ittuann/iGEM-2022-NEFU_China/Code/Visual Identification Module/2.jpg

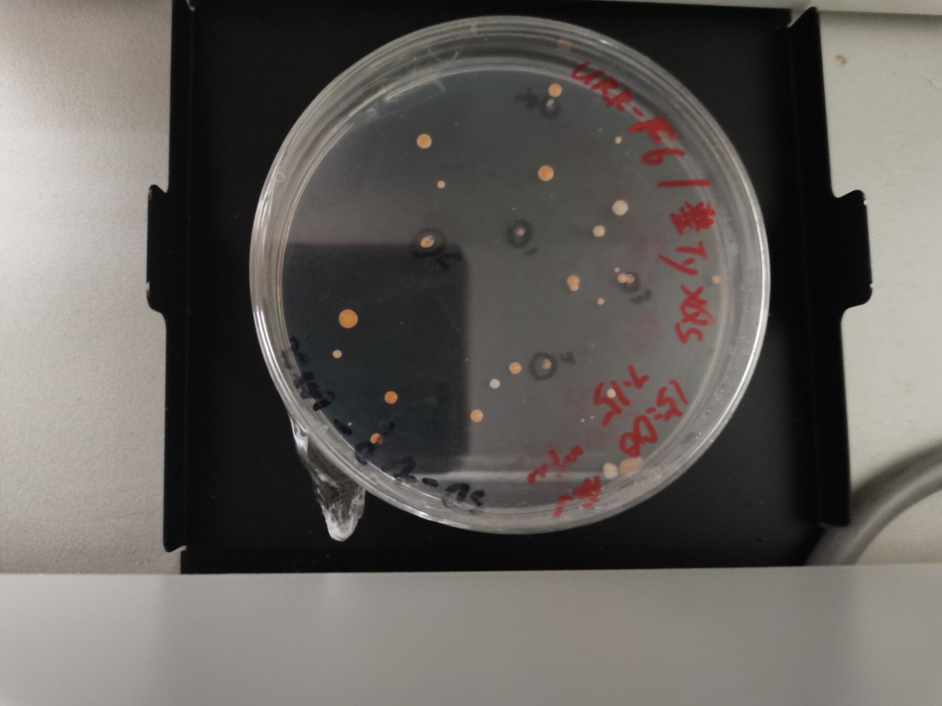
Code/Visual Identification Module/2.jpg
