ittuann/iGEM-2022-NEFU_China/Code/Visual Identification Module/11.jpg

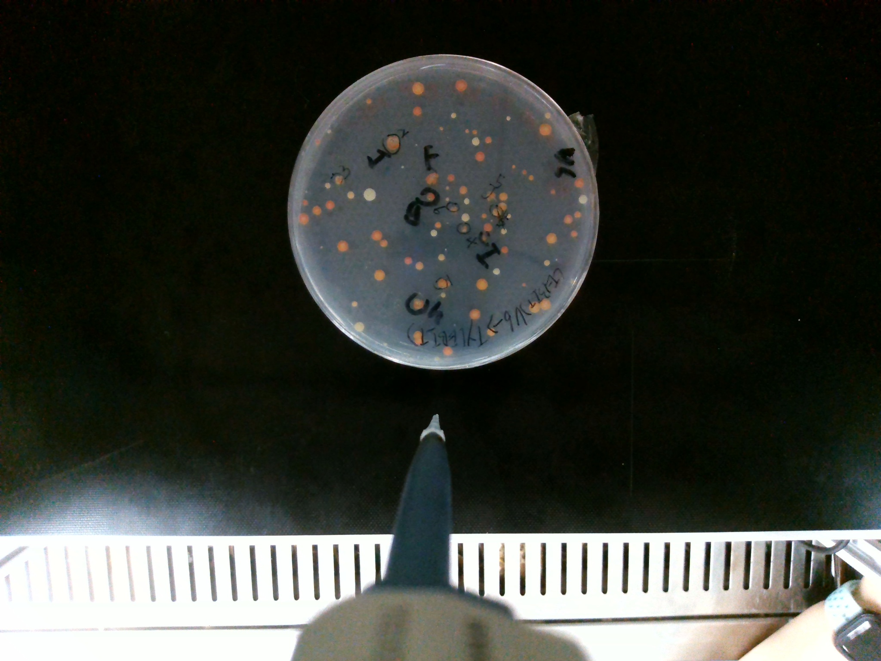
Code/Visual Identification Module/11.jpg
