ittuann/iGEM-2022-NEFU_China/Code/Visual Identification Module/13.jpg

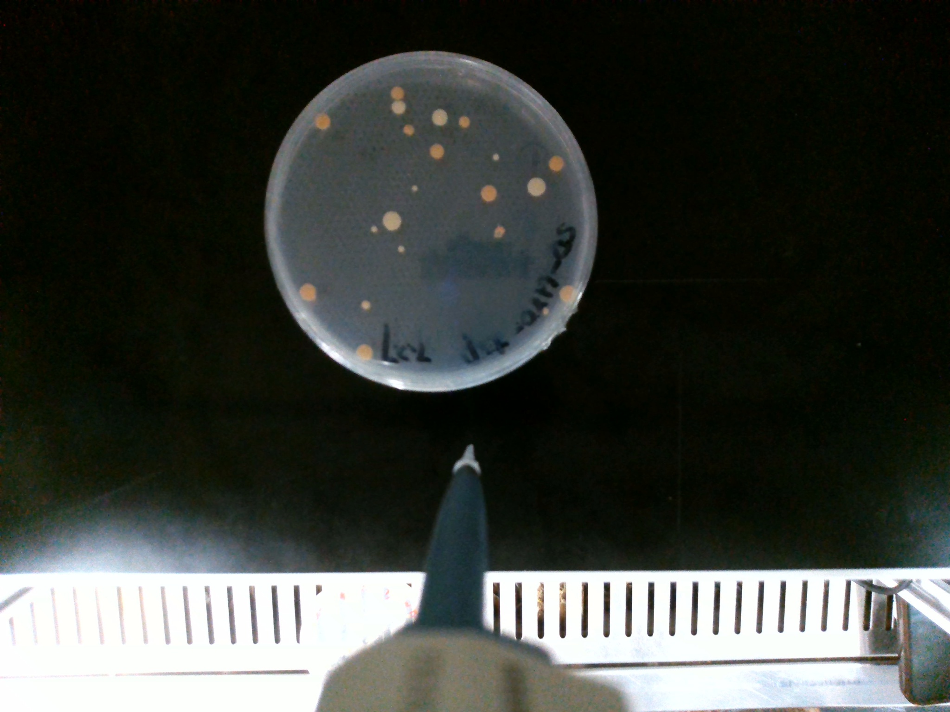
Code/Visual Identification Module/13.jpg
