ittuann/iGEM-2022-NEFU_China/Model/Project/圆盘组合A.SLDASM

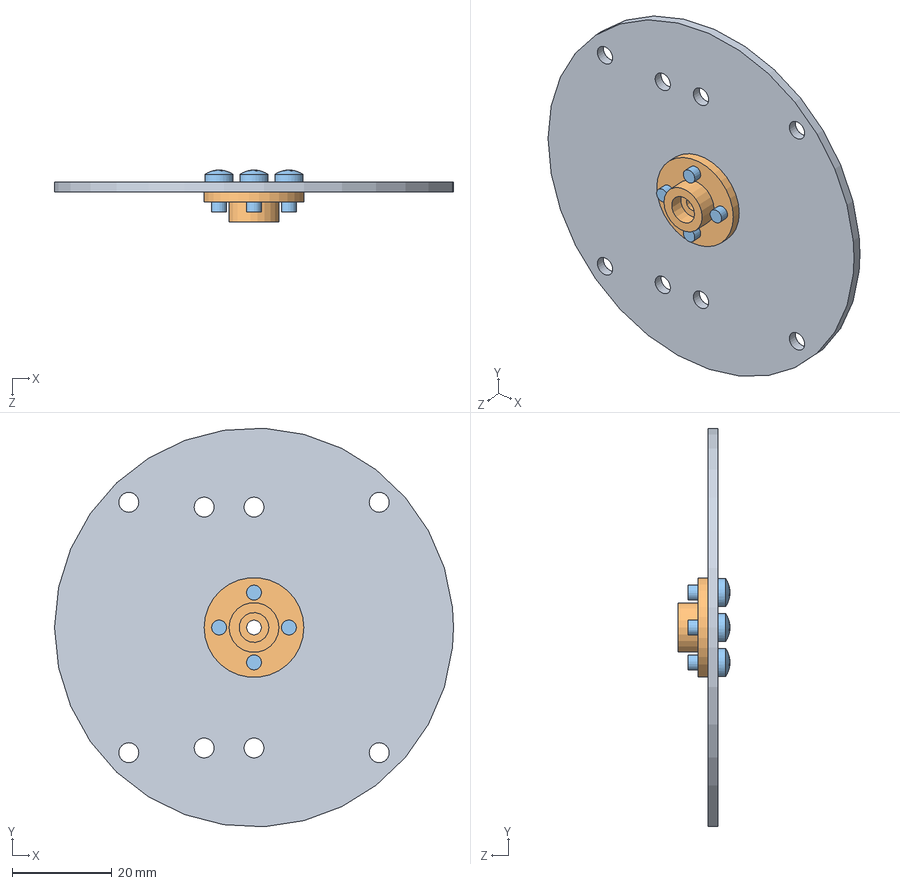
[picture p23: CAD file, 2022-10-12]
Model/Project/圆盘组合A.SLDASM
80.0 x 79.9 x 10.4 mm
小圆盘
金属舵盘
GB818-M3X6-ZN-4.8 x 4
