ittuann/iGEM-2022-NEFU_China/Model/Pipette Module.STL

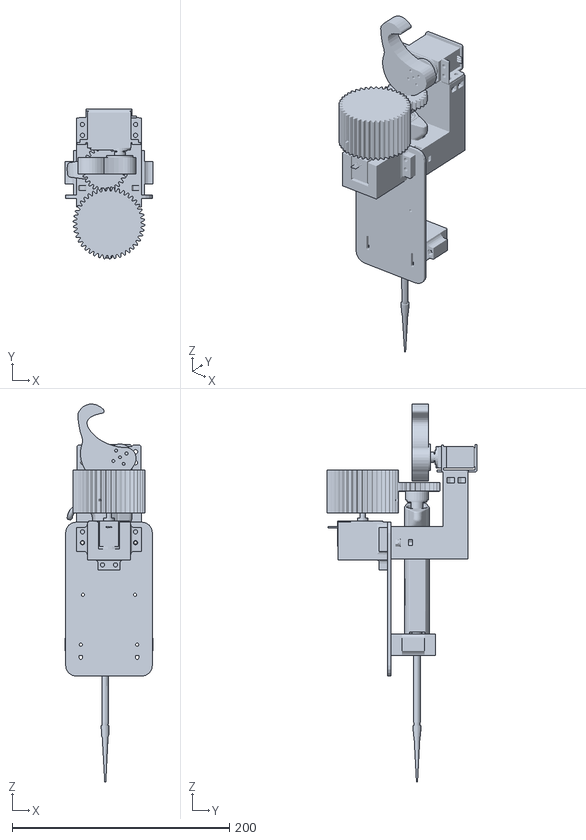
[picture p24: CAD file, 2022-10-11]
Model/Pipette Module.STL
81.0 x 138.3 x 348.2
