ittuann/iGEM-2022-NEFU_China/Model/Project/小舵机.SLDPRT

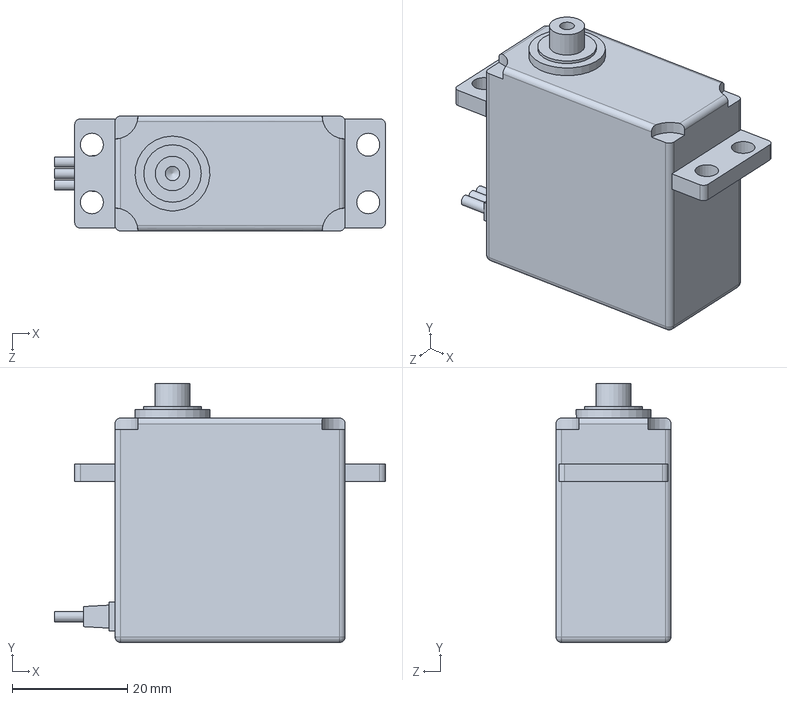
[picture p26: CAD file, 2022-10-12]
Model/Project/小舵机.SLDPRT
57.5 x 45.0 x 20.0 mm
