ittuann/iGEM-2022-NEFU_China/Model/Project/热端滑块.SLDPRT

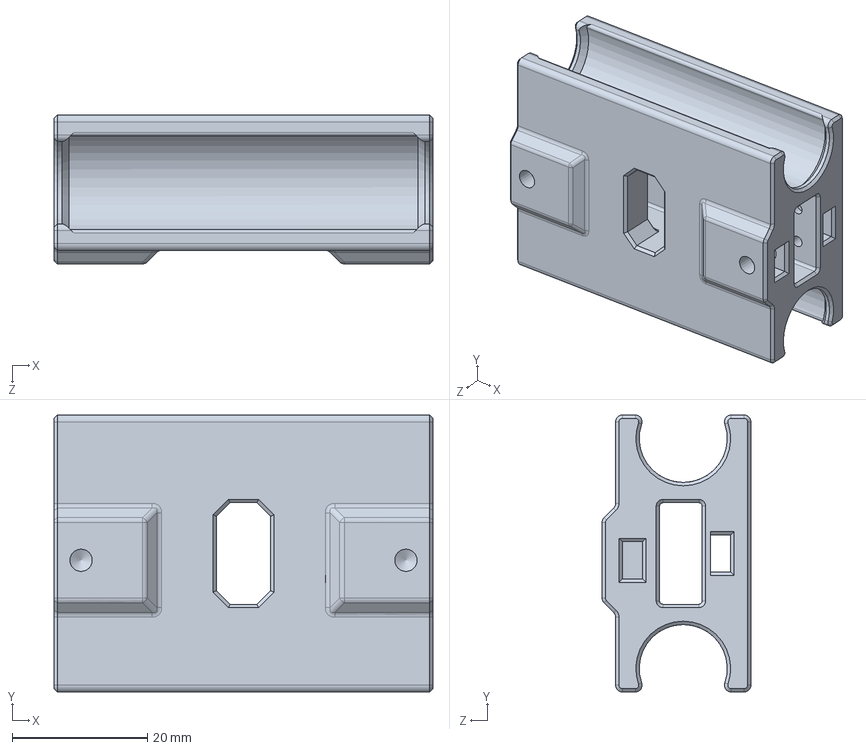
[picture p27: CAD file, 2022-10-12]
Model/Project/热端滑块.SLDPRT
56.0 x 40.9 x 22.0 mm
