ittuann/iGEM-2022-NEFU_China/Model/Project/221-BB-02-49 舵机座.SLDPRT

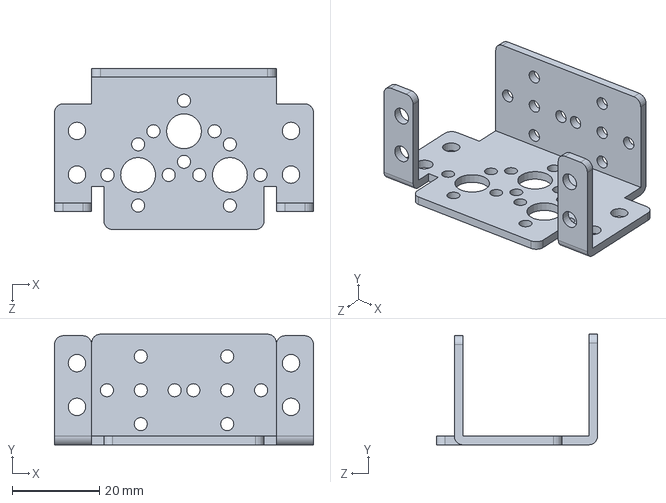
[picture p28: CAD file, 2022-10-12]
Model/Project/221-BB-02-49 舵机座.SLDPRT
59.3 x 25.4 x 36.9 mm
