ittuann/iGEM-2022-NEFU_China/Model/Project/GB818-M3X10-ZN-4.8.SLDPRT

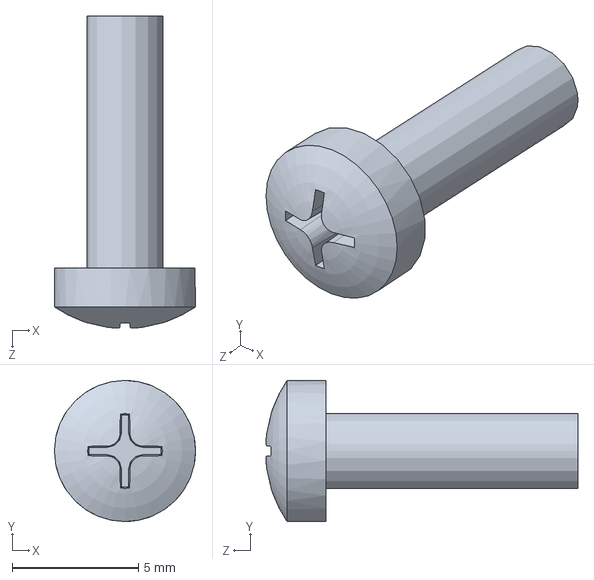
[picture p29: CAD file, 2022-10-12]
Model/Project/GB818-M3X10-ZN-4.8.SLDPRT
5.60 x 5.60 x 12.4 mm
