ittuann/iGEM-2022-NEFU_China/Model/Project/同步带2.SLDPRT

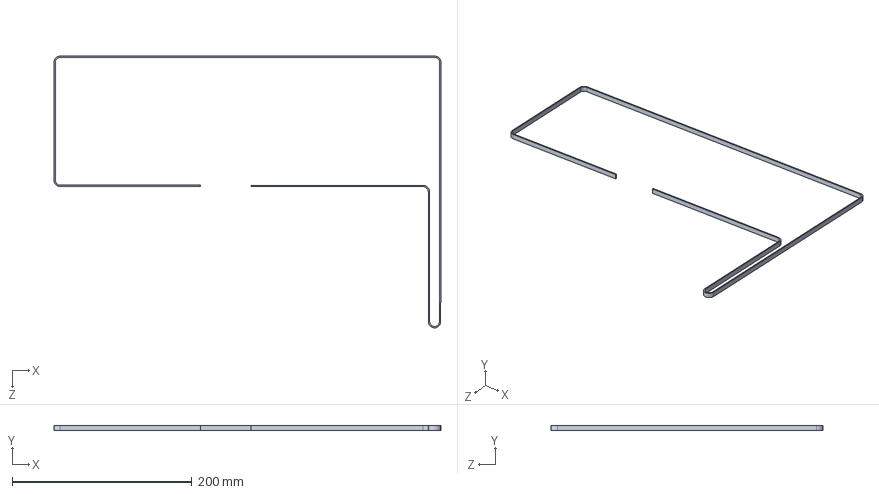
[picture p30: CAD file, 2022-10-12]
Model/Project/同步带2.SLDPRT
431.1 x 6.00 x 302.8 mm
