ittuann/iGEM-2022-NEFU_China/Model/Project/安装扣.SLDPRT

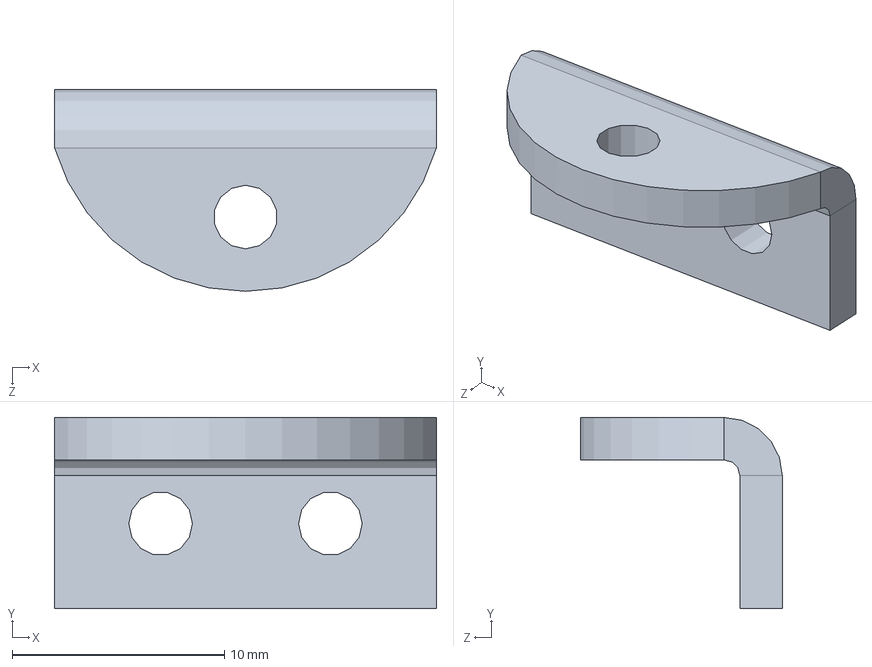
[picture p31: CAD file, 2022-10-12]
Model/Project/安装扣.SLDPRT
18.0 x 9.00 x 9.50 mm
