ittuann/iGEM-2022-NEFU_China/Model/Project/Корпус.SLDPRT

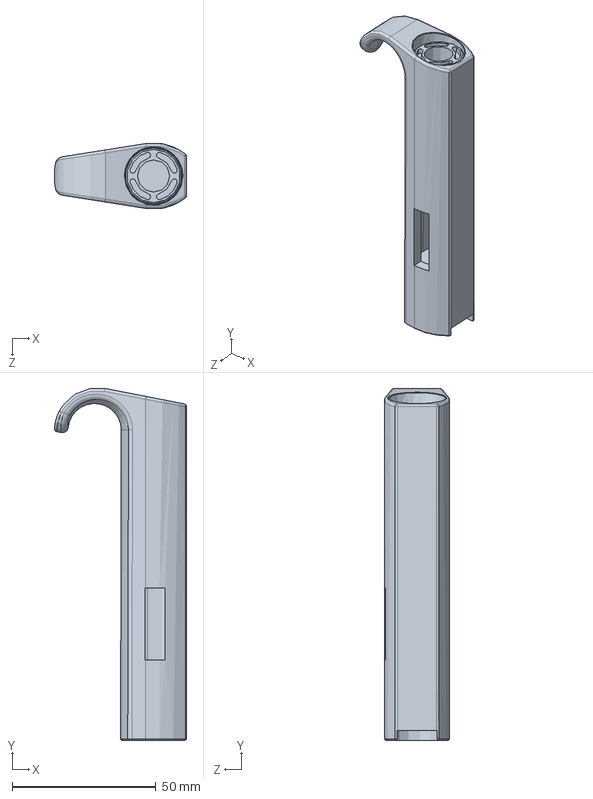
[picture p32: CAD file, 2022-10-12]
Model/Project/Корпус.SLDPRT
46.0 x 122.5 x 22.8 mm
