ittuann/iGEM-2022-NEFU_China/Model/Project/爪子齿轮.SLDPRT

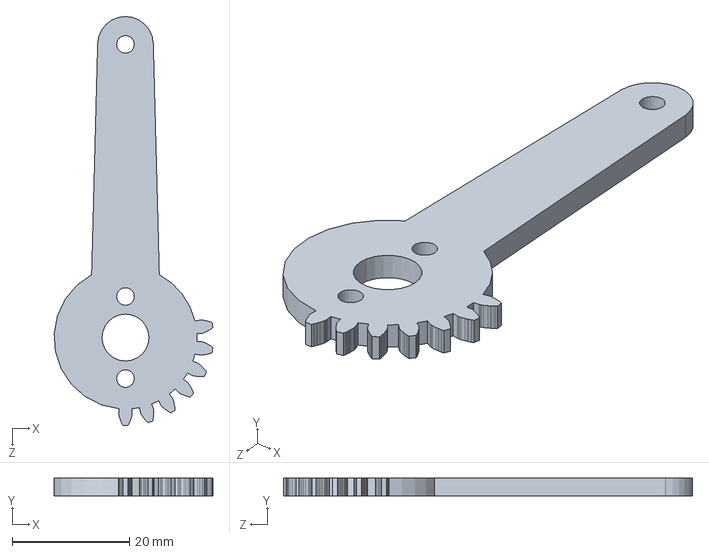
[picture p33: CAD file, 2022-10-12]
Model/Project/爪子齿轮.SLDPRT
27.1 x 3.00 x 69.7 mm
