ittuann/iGEM-2022-NEFU_China/Model/Project/JXS007.SLDPRT

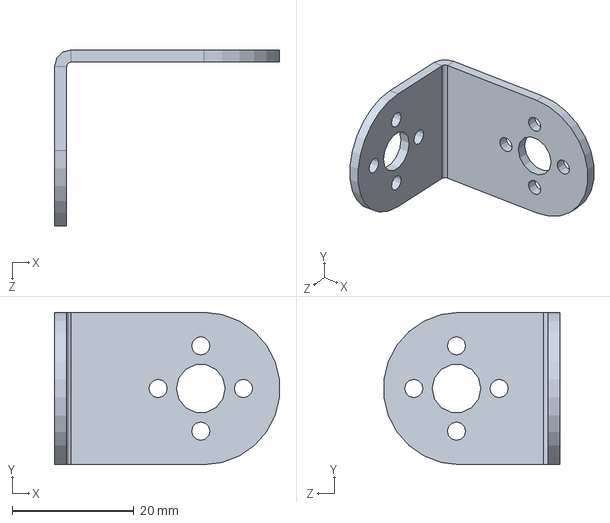
[picture p34: CAD file, 2022-10-12]
Model/Project/JXS007.SLDPRT
36.9 x 25.0 x 28.9 mm
