ittuann/iGEM-2022-NEFU_China/Model/Project/大轴承.SLDPRT

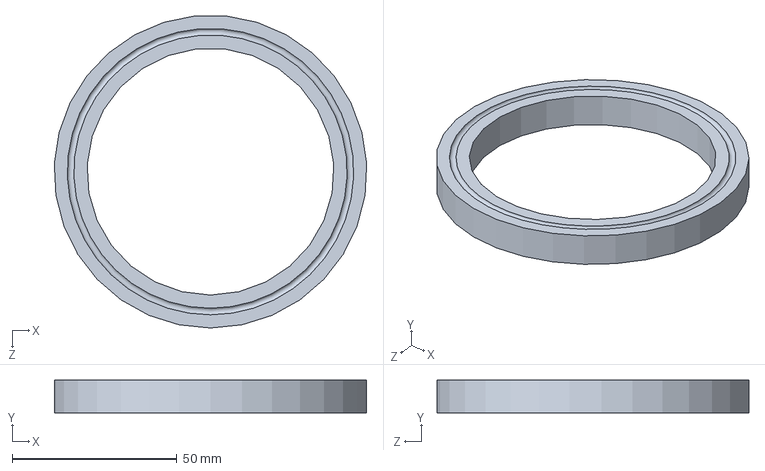
[picture p35: CAD file, 2022-10-12]
Model/Project/大轴承.SLDPRT
94.9 x 10.0 x 94.8 mm
