ittuann/iGEM-2022-NEFU_China/Model/Project/光轴支架_右上.SLDPRT

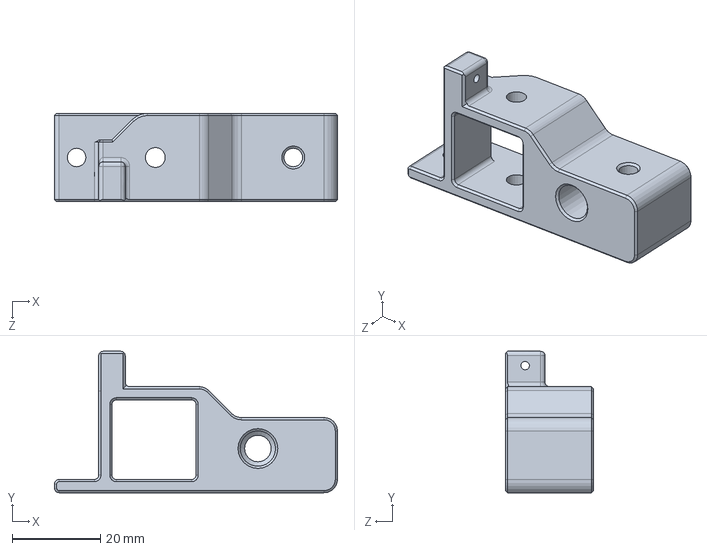
[picture p36: CAD file, 2022-10-12]
Model/Project/光轴支架_右上.SLDPRT
64.0 x 32.0 x 20.0 mm
