ittuann/iGEM-2022-NEFU_China/Model/Project/35BYJ电机座.SLDPRT

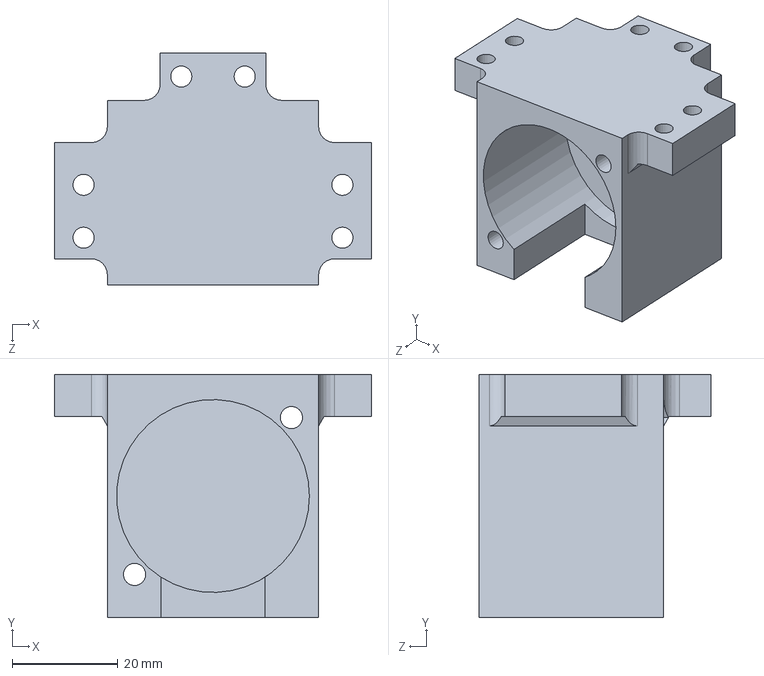
[picture p37: CAD file, 2022-10-12]
Model/Project/35BYJ电机座.SLDPRT
60.0 x 46.0 x 44.0 mm
