ittuann/iGEM-2022-NEFU_China/Model/Project/圆环.SLDPRT

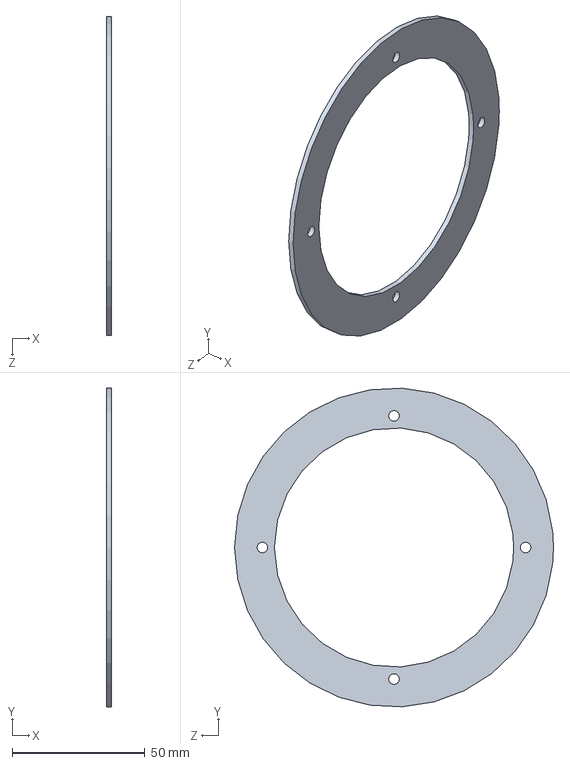
[picture p39: CAD file, 2022-10-12]
Model/Project/圆环.SLDPRT
2.00 x 119.8 x 120.0 mm
