ittuann/iGEM-2022-NEFU_China/Model/Project/大圆柱齿轮42×1.5.SLDPRT

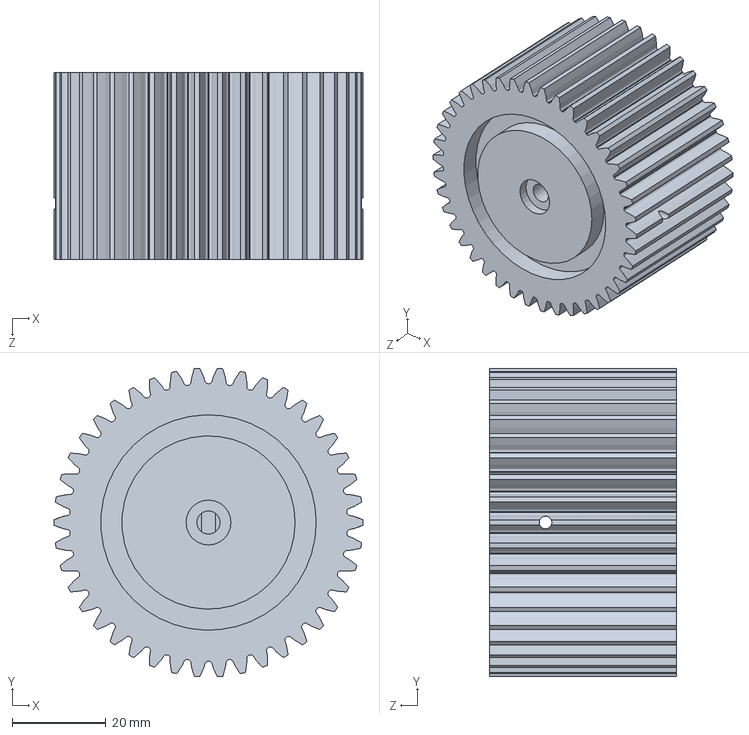
[picture p40: CAD file, 2022-10-12]
Model/Project/大圆柱齿轮42×1.5.SLDPRT
66.0 x 65.9 x 40.0 mm
