ittuann/iGEM-2022-NEFU_China/Model/Project/GB818-M3X14-ZN-4.8.SLDPRT

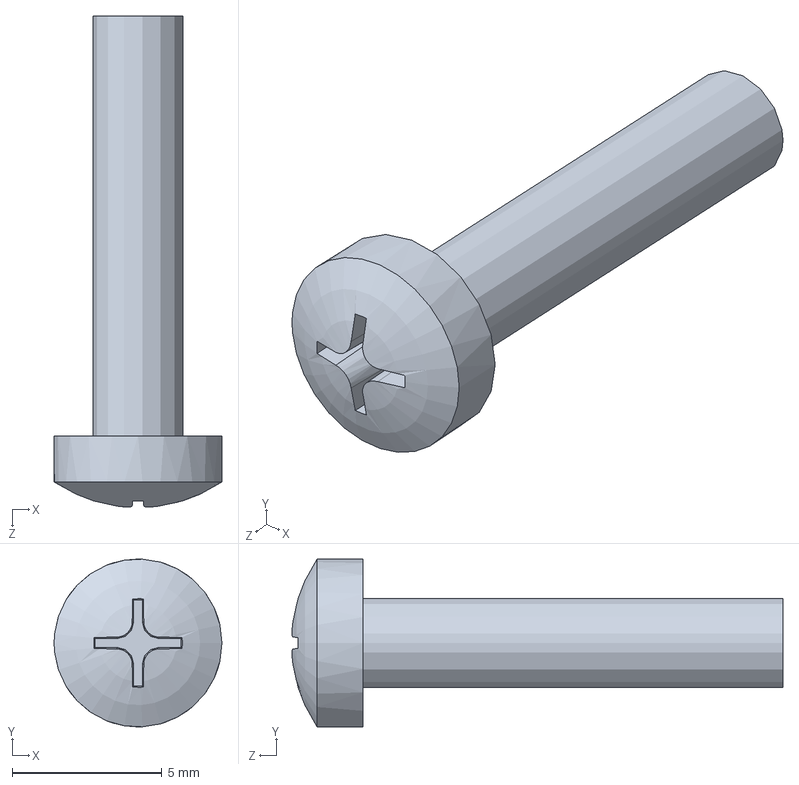
[picture p41: CAD file, 2022-10-12]
Model/Project/GB818-M3X14-ZN-4.8.SLDPRT
5.60 x 5.60 x 16.4 mm
