ittuann/iGEM-2022-NEFU_China/Model/Project/Z轴限位开关支架（2件）.SLDPRT

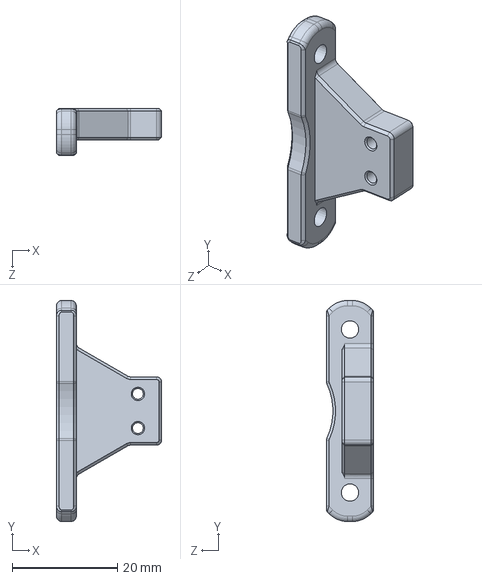
[picture p42: CAD file, 2022-10-12]
Model/Project/Z轴限位开关支架（2件）.SLDPRT
20.0 x 42.0 x 9.00 mm
