ittuann/iGEM-2022-NEFU_China/Model/Project/Кнопка экстрактора.SLDPRT

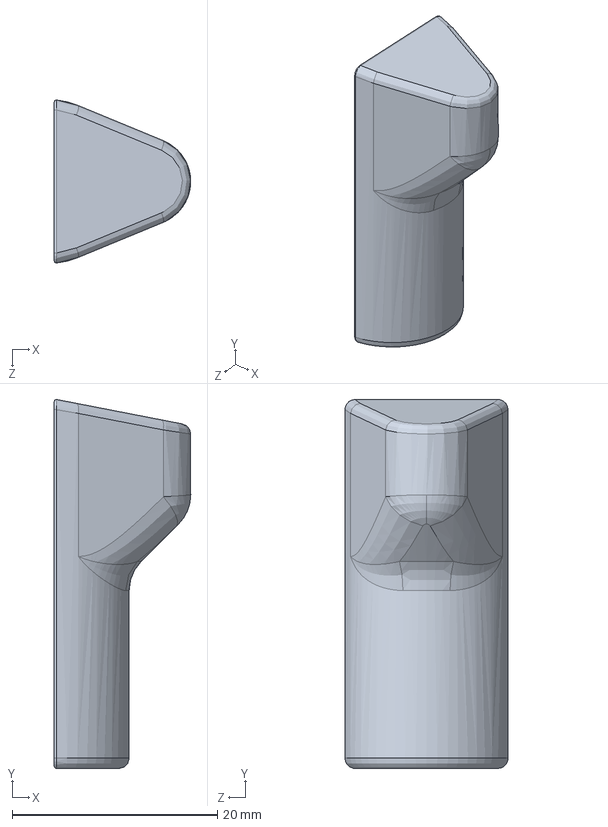
[picture p44: CAD file, 2022-10-12]
Model/Project/Кнопка экстрактора.SLDPRT
13.3 x 36.0 x 15.9 mm
