ittuann/iGEM-2022-NEFU_China/Model/Project/长杆.SLDPRT

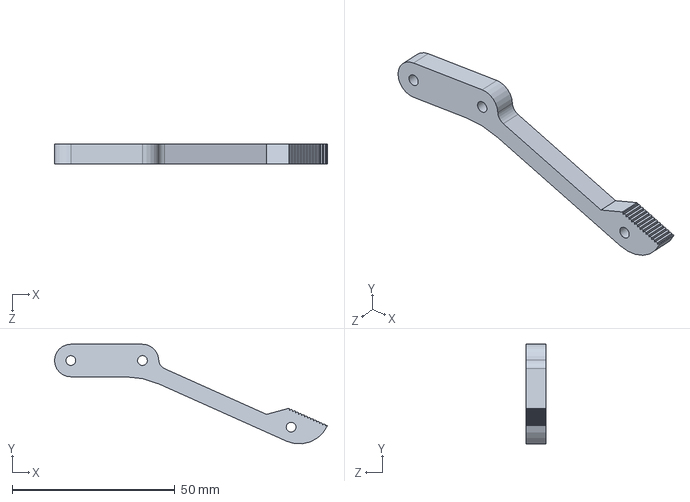
[picture p45: CAD file, 2022-10-12]
Model/Project/长杆.SLDPRT
83.8 x 30.5 x 6.00 mm
