ittuann/iGEM-2022-NEFU_China/Model/Project/光轴支架_左下.SLDPRT

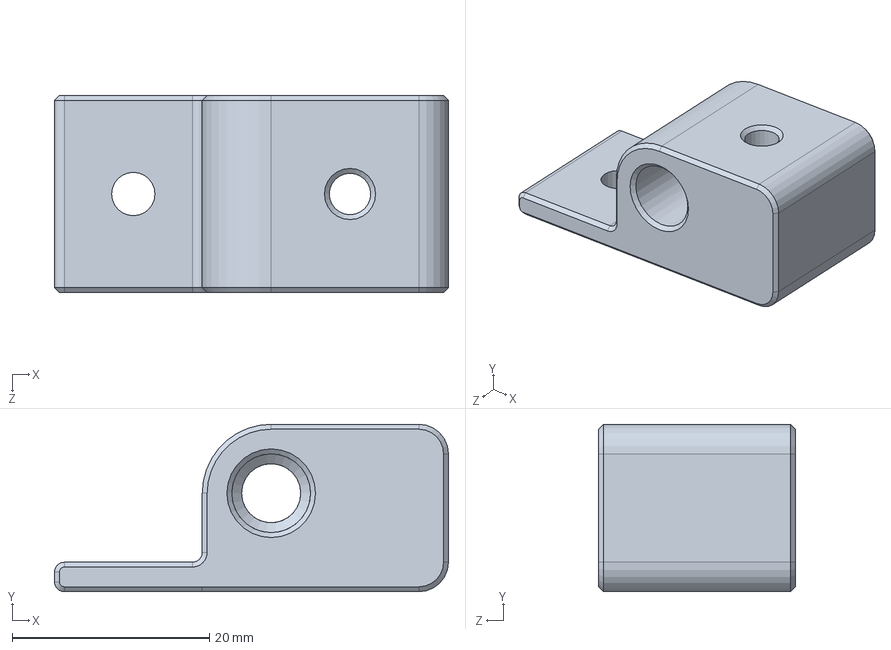
[picture p46: CAD file, 2022-10-12]
Model/Project/光轴支架_左下.SLDPRT
40.0 x 17.0 x 20.0 mm
