ittuann/iGEM-2022-NEFU_China/Model/Project/X轴光轴座_右.SLDPRT

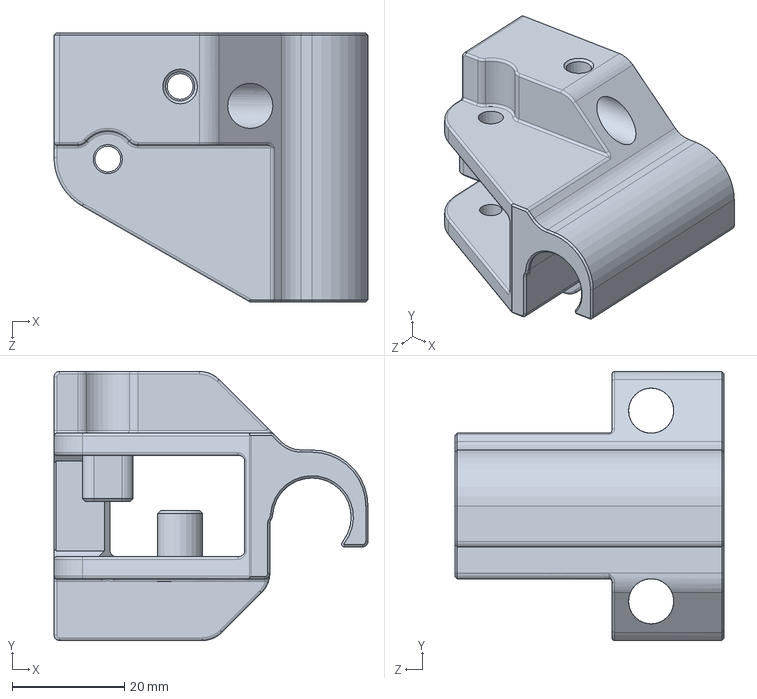
[picture p47: CAD file, 2022-10-12]
Model/Project/X轴光轴座_右.SLDPRT
56.0 x 48.0 x 48.0 mm
