ittuann/iGEM-2022-NEFU_China/Model/Project/圆柱齿轮小.SLDPRT

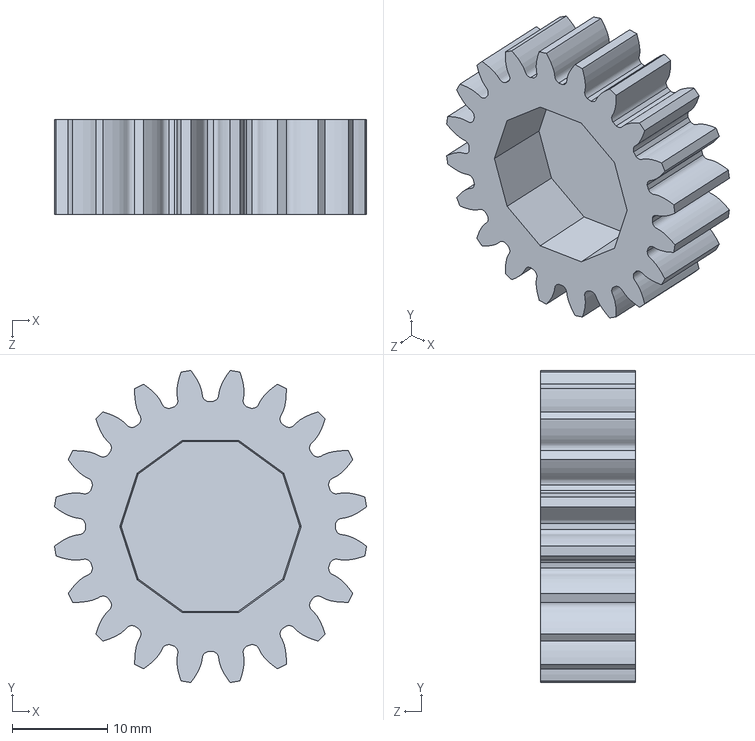
[picture p48: CAD file, 2022-10-12]
Model/Project/圆柱齿轮小.SLDPRT
32.7 x 32.7 x 10.0 mm
