ittuann/iGEM-2022-NEFU_China/Model/Project/JXS005.SLDPRT

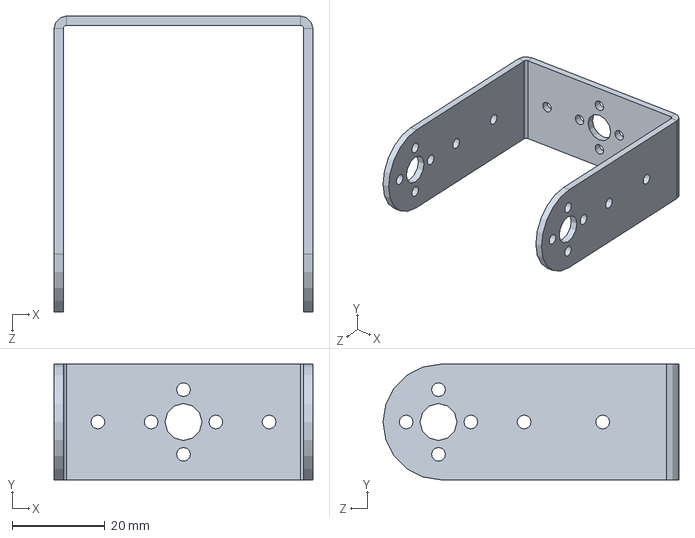
[picture p49: CAD file, 2022-10-12]
Model/Project/JXS005.SLDPRT
56.0 x 25.0 x 64.0 mm
