ittuann/iGEM-2022-NEFU_China/Model/Project/小横杆.SLDPRT

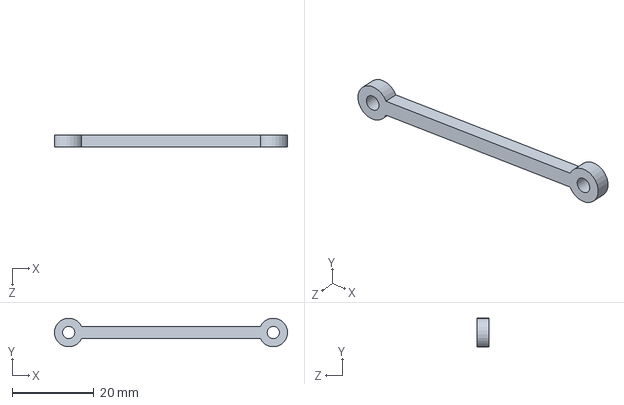
[picture p50: CAD file, 2022-10-12]
Model/Project/小横杆.SLDPRT
56.9 x 6.97 x 3.00 mm
