ittuann/iGEM-2022-NEFU_China/Model/Project/42步进电机.SLDPRT

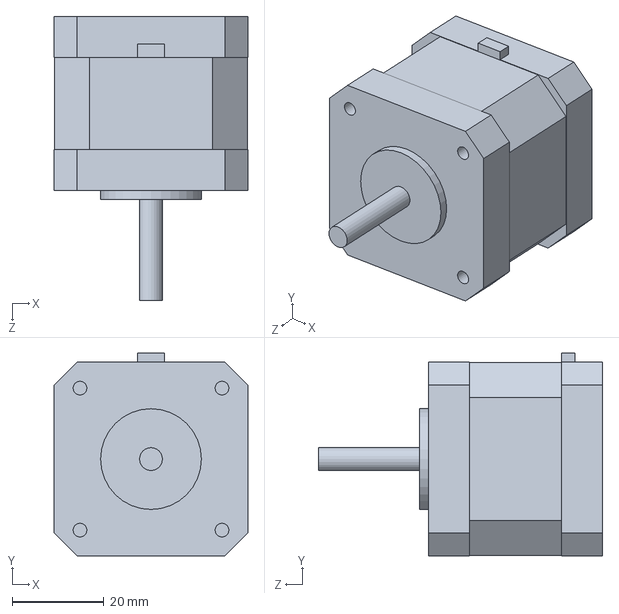
[picture p52: CAD file, 2022-10-12]
Model/Project/42步进电机.SLDPRT
42.3 x 44.3 x 62.0 mm
