ittuann/iGEM-2022-NEFU_China/Model/Project/小圆盘.SLDPRT

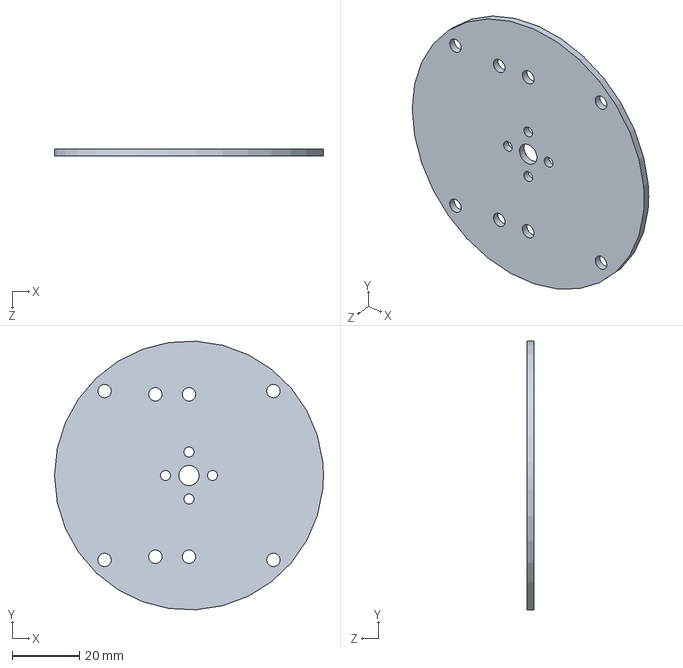
[picture p53: CAD file, 2022-10-12]
Model/Project/小圆盘.SLDPRT
80.0 x 79.9 x 2.00 mm
