ittuann/iGEM-2022-NEFU_China/Model/Project/舵机连接独立.SLDPRT

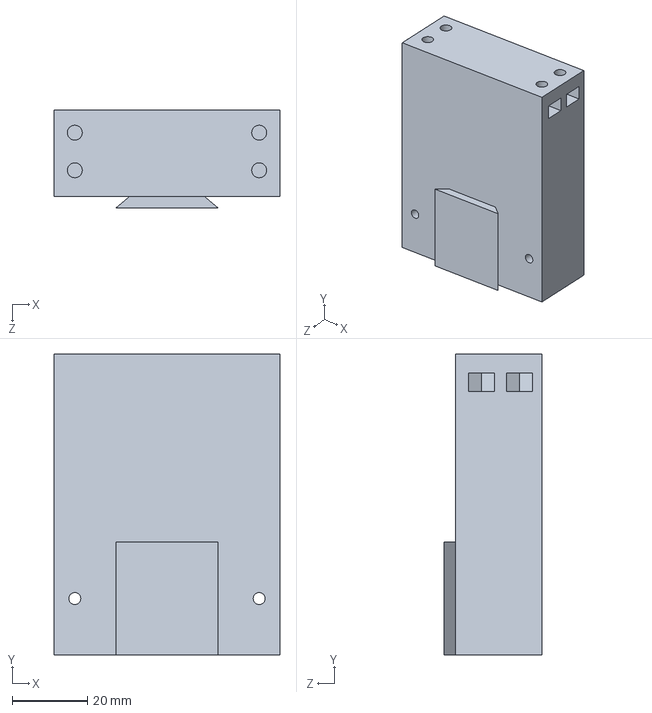
[picture p54: CAD file, 2022-10-12]
Model/Project/舵机连接独立.SLDPRT
60.0 x 80.0 x 26.0 mm
