ittuann/iGEM-2022-NEFU_China/Model/Project/圆柱齿轮26×1.5.SLDPRT

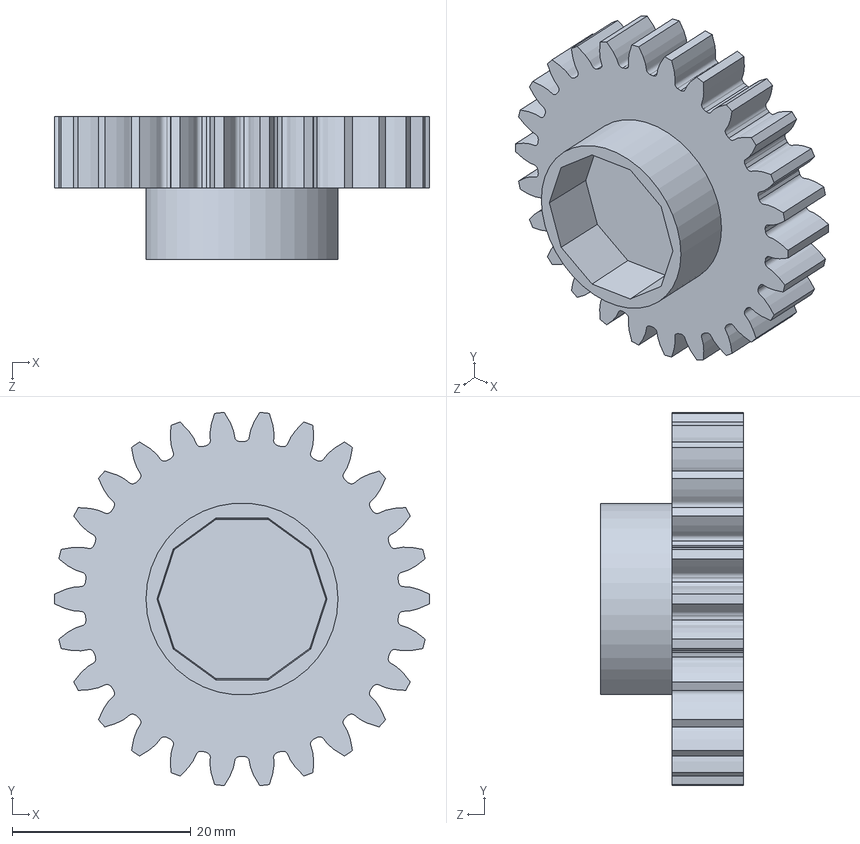
[picture p55: CAD file, 2022-10-12]
Model/Project/圆柱齿轮26×1.5.SLDPRT
42.0 x 41.8 x 16.0 mm
