ittuann/iGEM-2022-NEFU_China/Model/Project/小垫片.SLDPRT

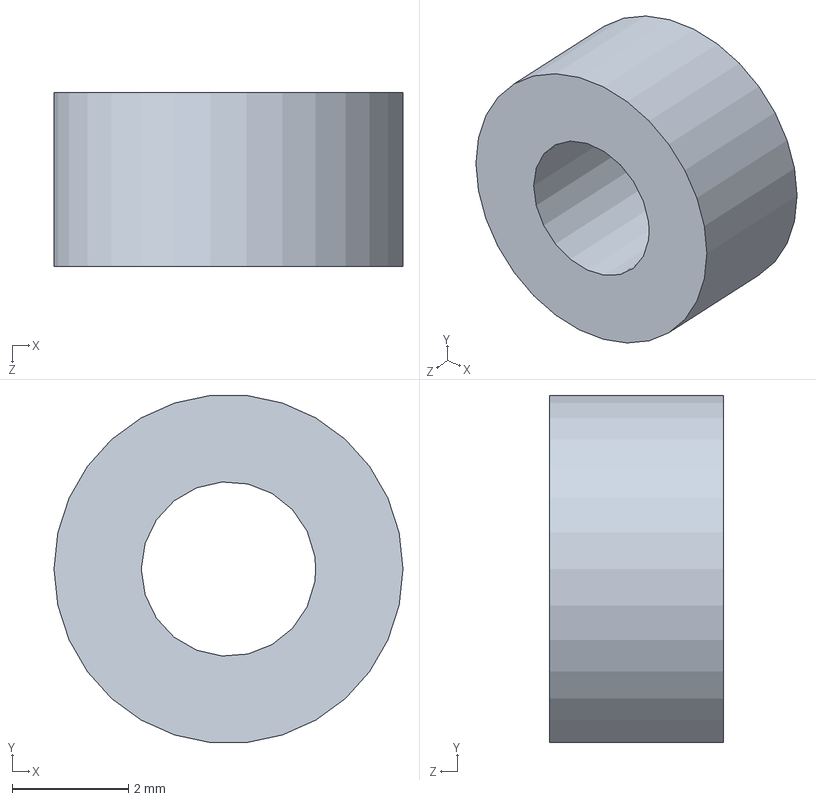
[picture p56: CAD file, 2022-10-12]
Model/Project/小垫片.SLDPRT
6.00 x 5.97 x 3.00 mm
