ittuann/iGEM-2022-NEFU_China/Model/Project/中心配重块.SLDPRT

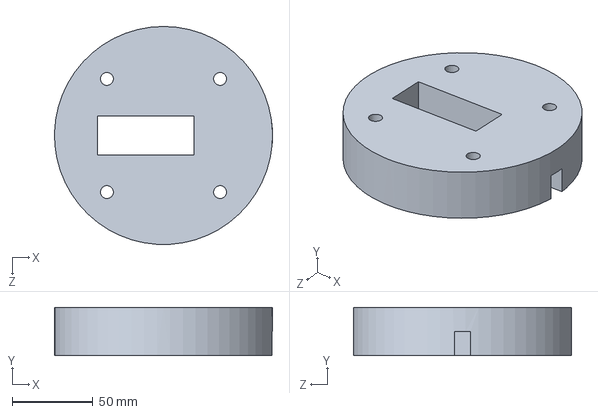
[picture p57: CAD file, 2022-10-12]
Model/Project/中心配重块.SLDPRT
134.9 x 30.0 x 135.0 mm
