ittuann/iGEM-2022-NEFU_China/Model/Project/连接板.SLDPRT

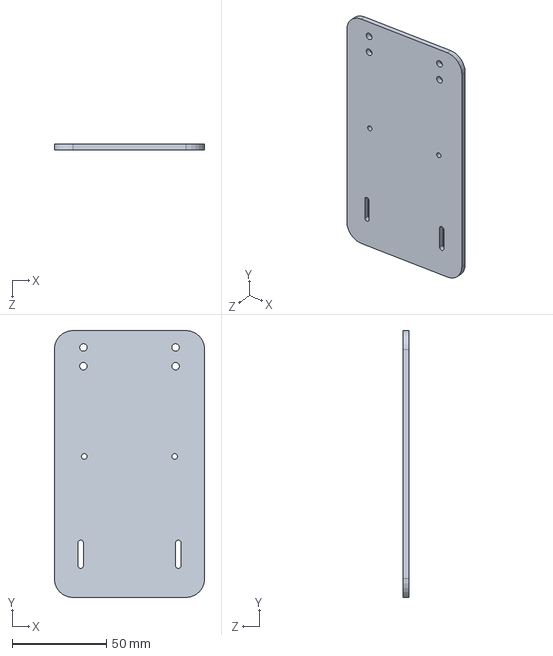
[picture p58: CAD file, 2022-10-12]
Model/Project/连接板.SLDPRT
80.0 x 142.0 x 3.00 mm
