ittuann/iGEM-2022-NEFU_China/Model/Project/底板.SLDPRT

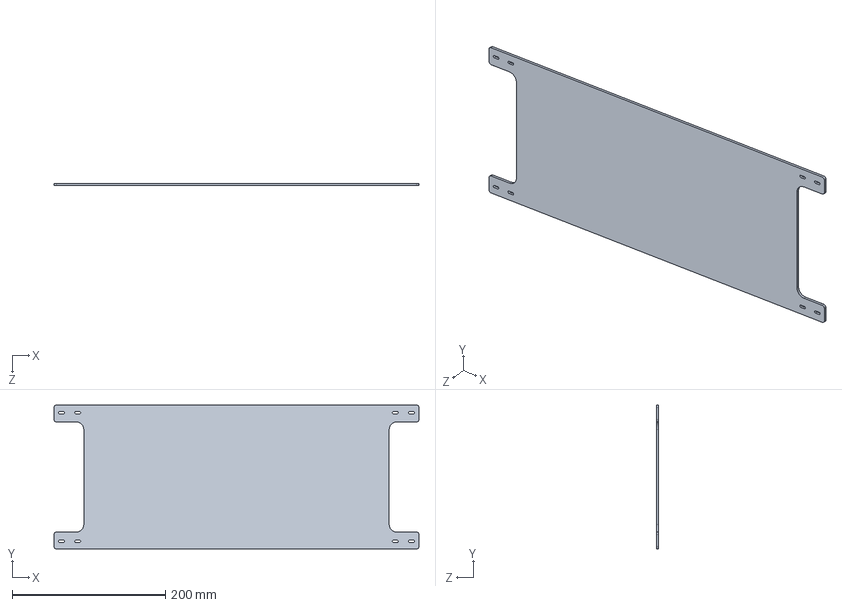
[picture p59: CAD file, 2022-10-12]
Model/Project/底板.SLDPRT
477.0 x 188.0 x 3.00 mm
