ittuann/iGEM-2022-NEFU_China/Model/Project/中心配重块上层.SLDPRT

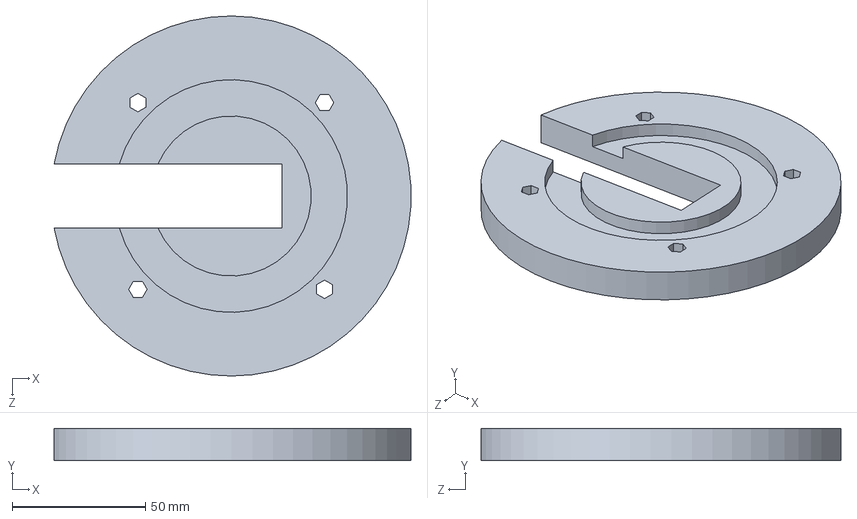
[picture p60: CAD file, 2022-10-12]
Model/Project/中心配重块上层.SLDPRT
133.8 x 12.0 x 135.0 mm
