ittuann/iGEM-2022-NEFU_China/Model/Project/Игла.SLDPRT

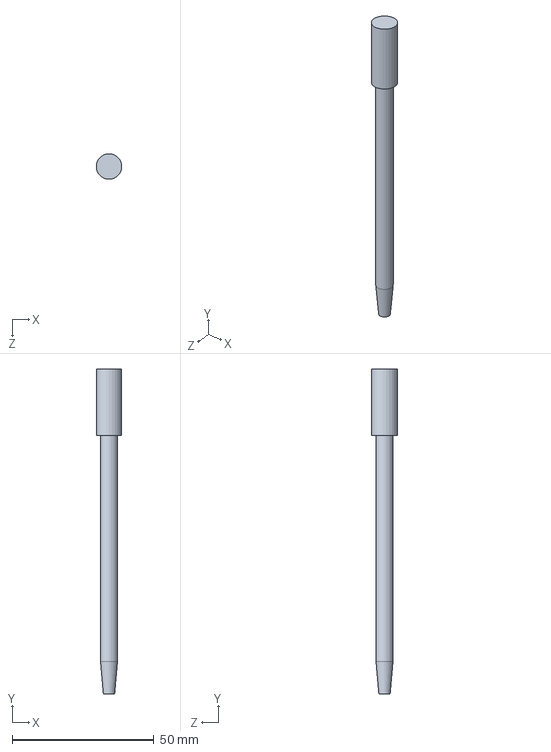
[picture p61: CAD file, 2022-10-12]
Model/Project/Игла.SLDPRT
8.93 x 114.5 x 9.00 mm
