ittuann/iGEM-2022-NEFU_China/Model/Project/Наконечник иглы.SLDPRT

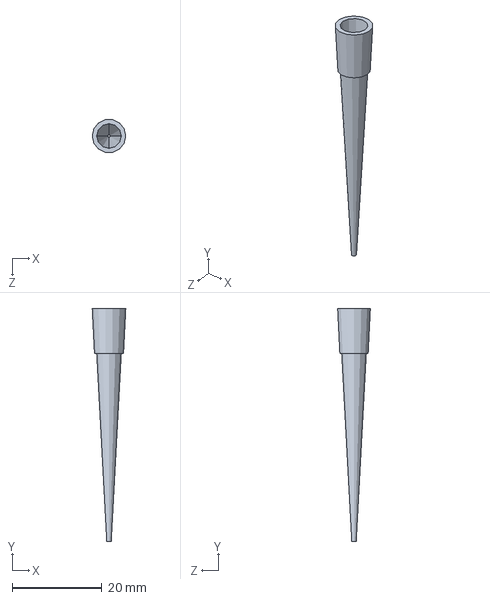
[picture p62: CAD file, 2022-10-12]
Model/Project/Наконечник иглы.SLDPRT
7.50 x 52.0 x 7.31 mm
