ittuann/iGEM-2022-NEFU_China/Model/Project/铝基板热床200×300×3.SLDPRT

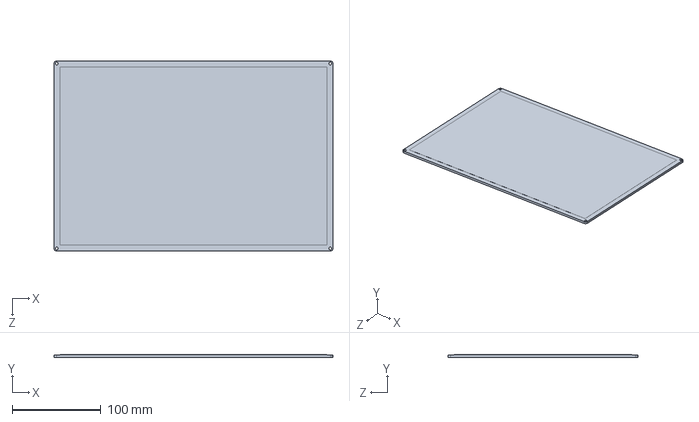
[picture p63: CAD file, 2022-10-12]
Model/Project/铝基板热床200×300×3.SLDPRT
314.0 x 3.20 x 214.0 mm
