ittuann/iGEM-2022-NEFU_China/Model/Project/杯士轴承.SLDPRT

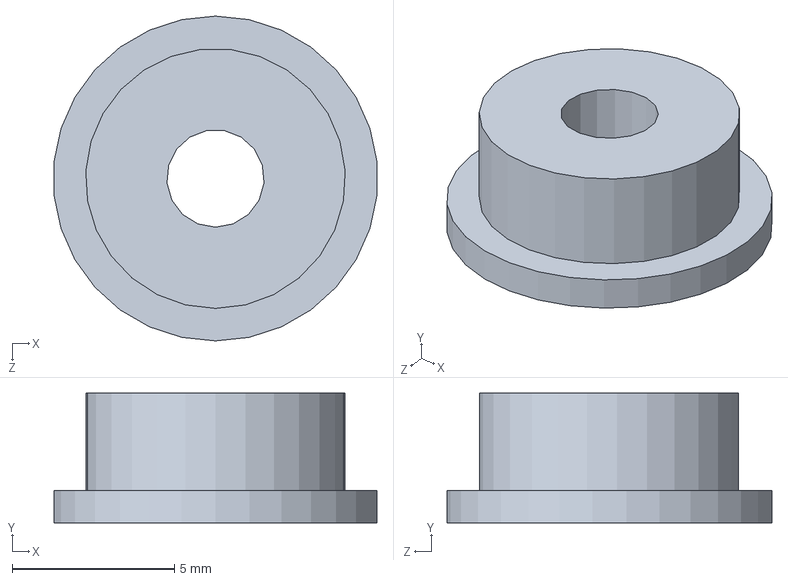
[picture p64: CAD file, 2022-10-12]
Model/Project/杯士轴承.SLDPRT
9.95 x 4.00 x 10.0 mm
