ittuann/iGEM-2022-NEFU_China/Model/Project/35BYJ412.SLDPRT

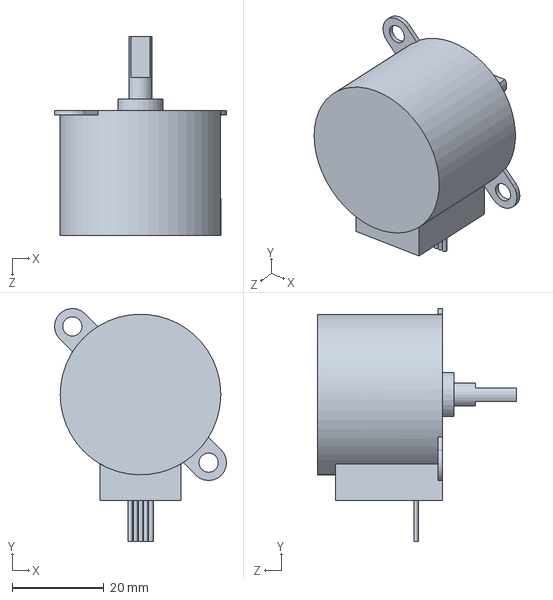
[picture p65: CAD file, 2022-10-12]
Model/Project/35BYJ412.SLDPRT
37.5 x 50.8 x 43.4 mm
