ittuann/iGEM-2022-NEFU_China/Model/Project/底部圆盘.SLDPRT

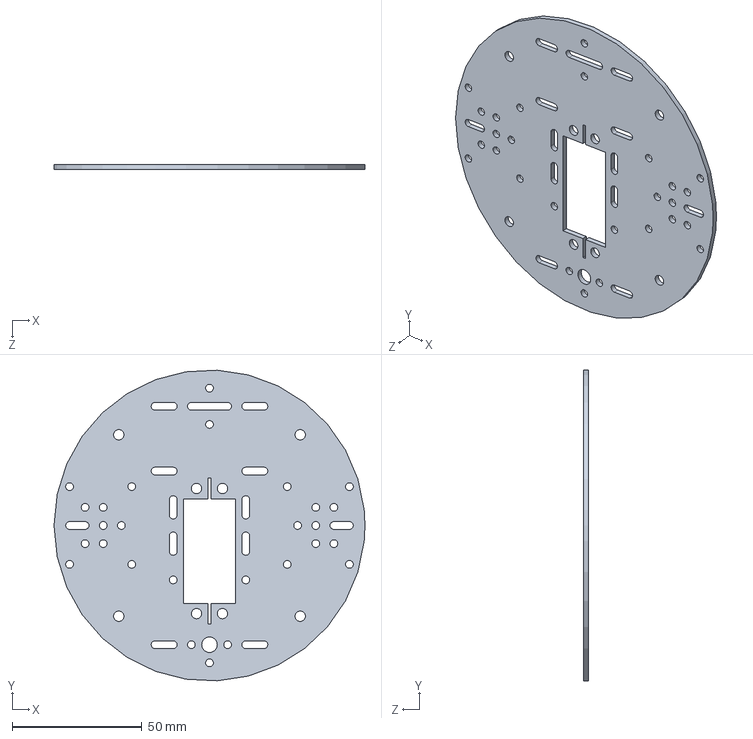
[picture p66: CAD file, 2022-10-12]
Model/Project/底部圆盘.SLDPRT
120.0 x 119.8 x 2.00 mm
