ittuann/iGEM-2022-NEFU_China/Model/Project/惠普电源DPS-460EB A.SLDPRT

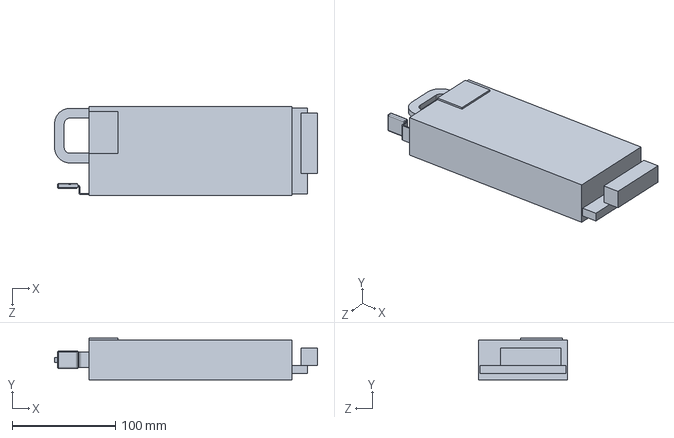
[picture p67: CAD file, 2022-10-12]
Model/Project/惠普电源DPS-460EB A.SLDPRT
254.5 x 40.5 x 86.5 mm
