ittuann/iGEM-2022-NEFU_China/Model/Project/螺柱.SLDPRT

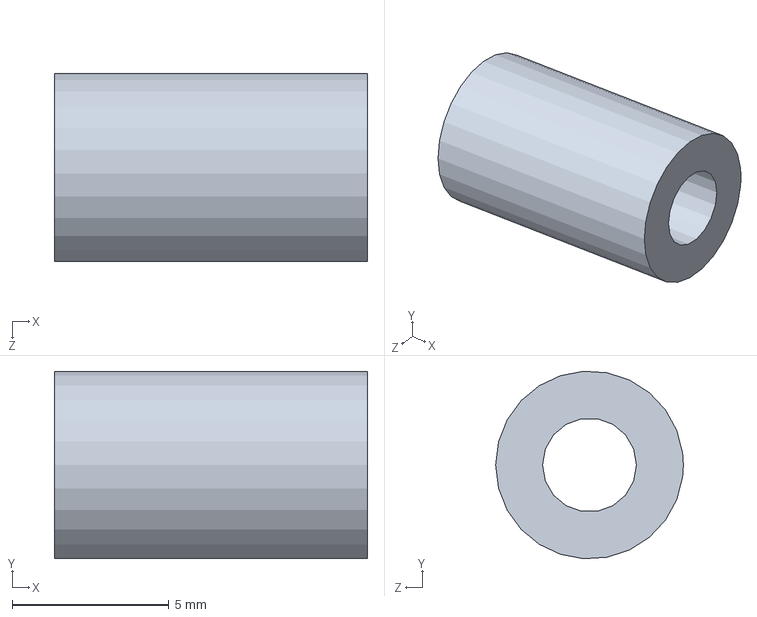
[picture p68: CAD file, 2022-10-12]
Model/Project/螺柱.SLDPRT
10.0 x 5.99 x 6.00 mm
