ittuann/iGEM-2022-NEFU_China/Model/Project/大底板.SLDPRT

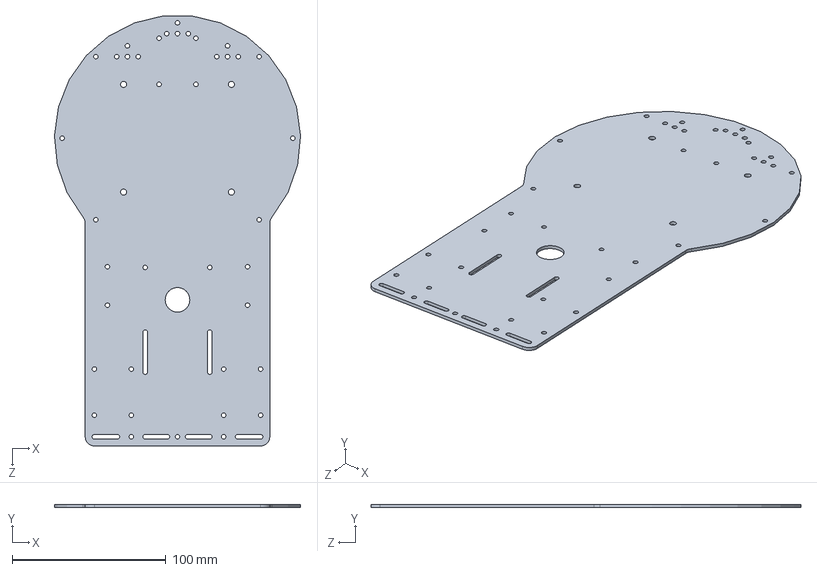
[picture p69: CAD file, 2022-10-12]
Model/Project/大底板.SLDPRT
160.0 x 2.00 x 279.4 mm
