ittuann/iGEM-2022-NEFU_China/Model/Project/双向凸轮.SLDPRT

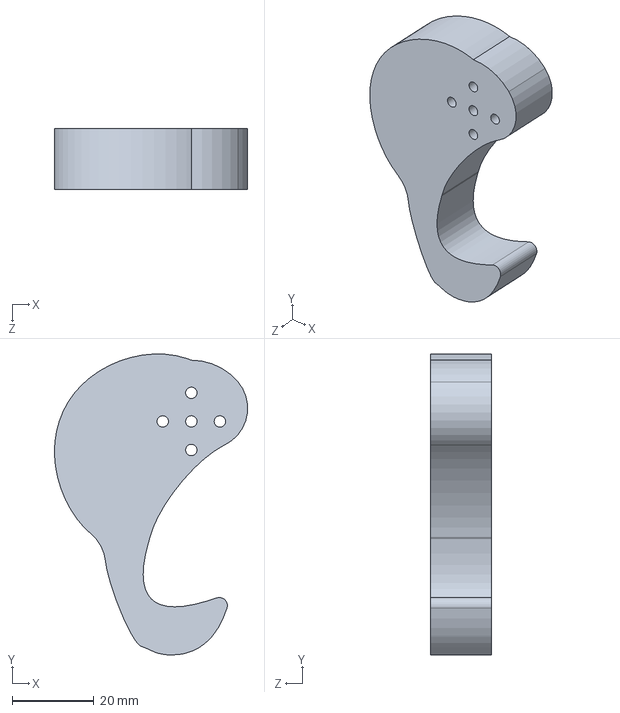
[picture p70: CAD file, 2022-10-12]
Model/Project/双向凸轮.SLDPRT
47.3 x 73.7 x 15.0 mm
