ittuann/iGEM-2022-NEFU_China/Model/Project/舵机外壳.SLDPRT

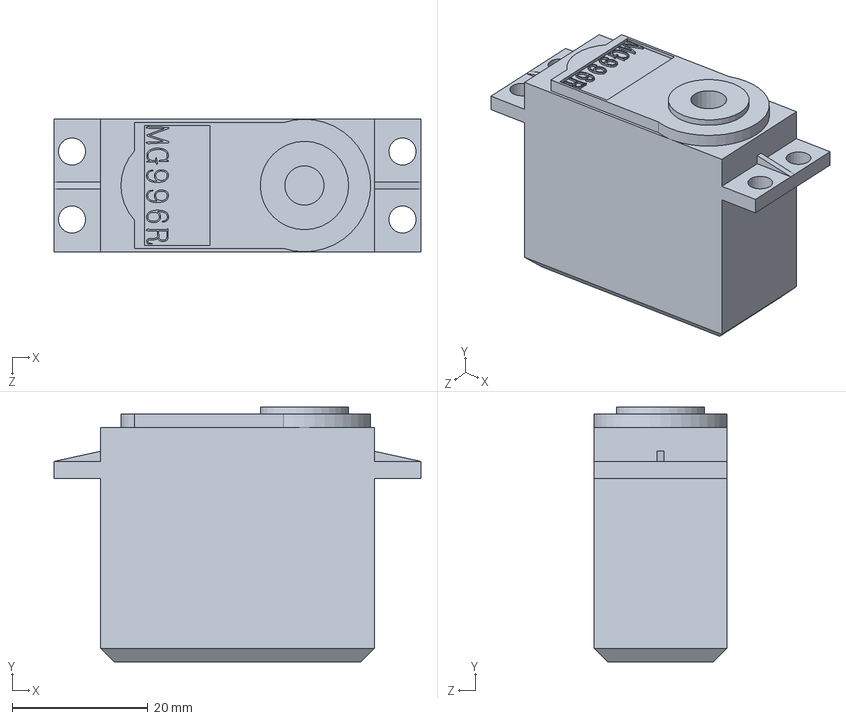
[picture p71: CAD file, 2022-10-12]
Model/Project/舵机外壳.SLDPRT
54.0 x 37.5 x 19.5 mm
