ittuann/iGEM-2022-NEFU_China/Model/Project/大圆盘.SLDPRT

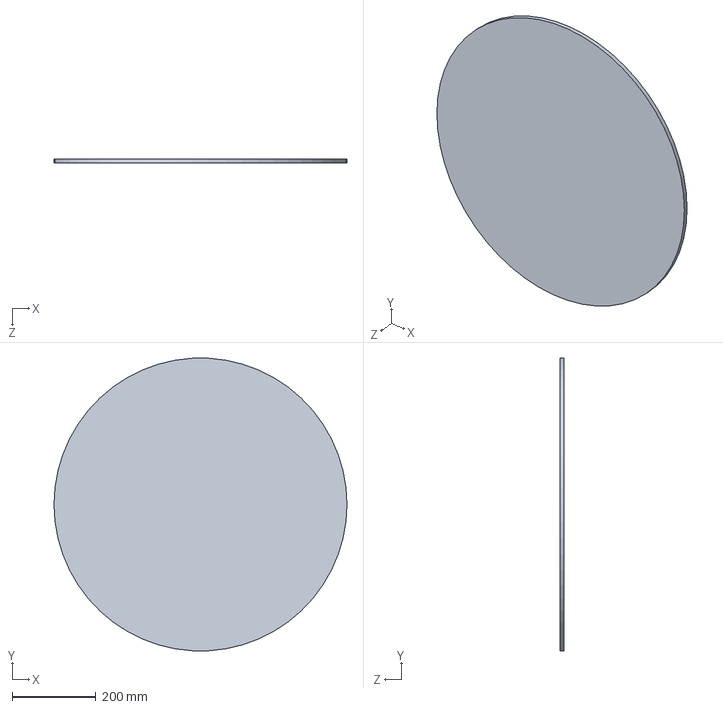
[picture p72: CAD file, 2022-10-12]
Model/Project/大圆盘.SLDPRT
700.0 x 698.8 x 10.0 mm
