ittuann/iGEM-2022-NEFU_China/Model/Project/叠加零件X6.SLDPRT

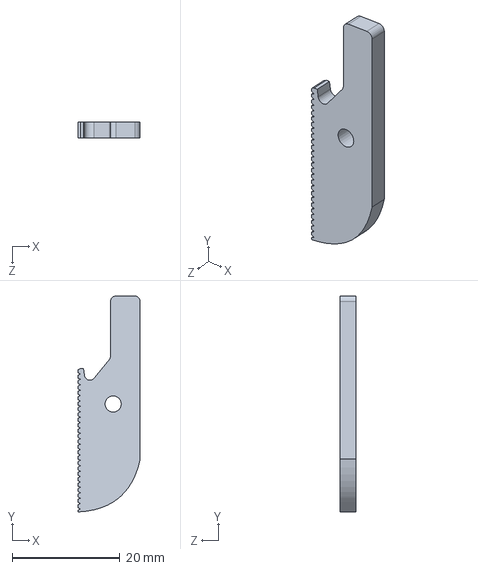
[picture p73: CAD file, 2022-10-12]
Model/Project/叠加零件X6.SLDPRT
11.6 x 40.0 x 3.00 mm
