ittuann/iGEM-2022-NEFU_China/Model/Project/手爪 （新）.SLDPRT

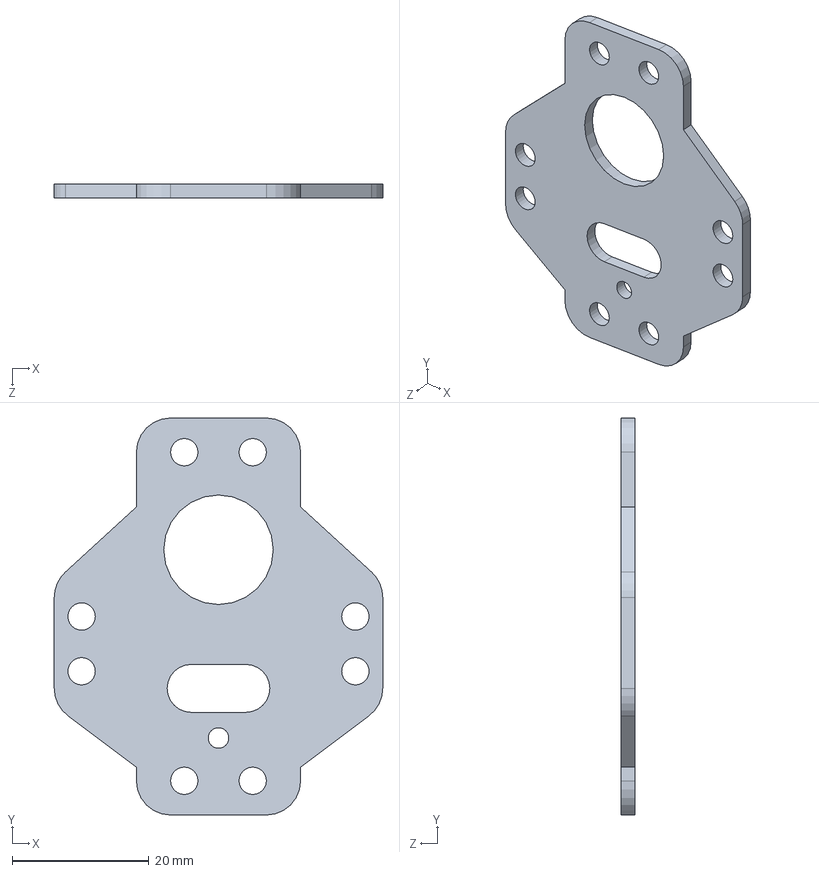
[picture p74: CAD file, 2022-10-12]
Model/Project/手爪 （新）.SLDPRT
48.0 x 58.0 x 2.00 mm
