ittuann/iGEM-2022-NEFU_China/Model/Project/舵机轴.SLDPRT

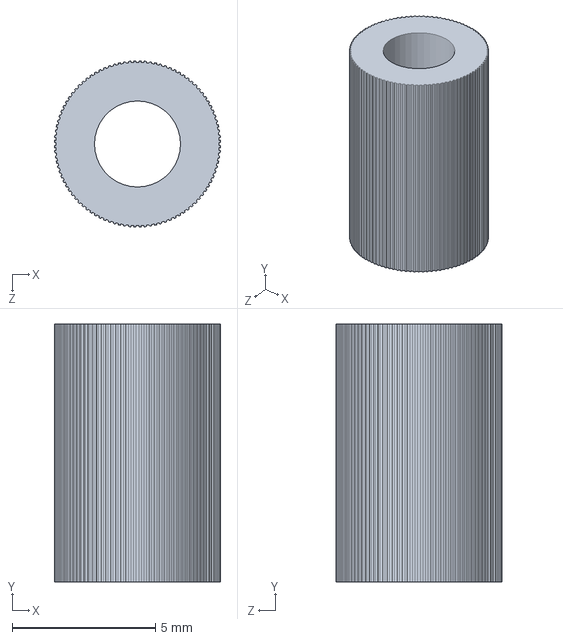
[picture p75: CAD file, 2022-10-12]
Model/Project/舵机轴.SLDPRT
5.80 x 9.00 x 5.80 mm
