ittuann/iGEM-2022-NEFU_China/Model/Project/Кнопка.SLDPRT

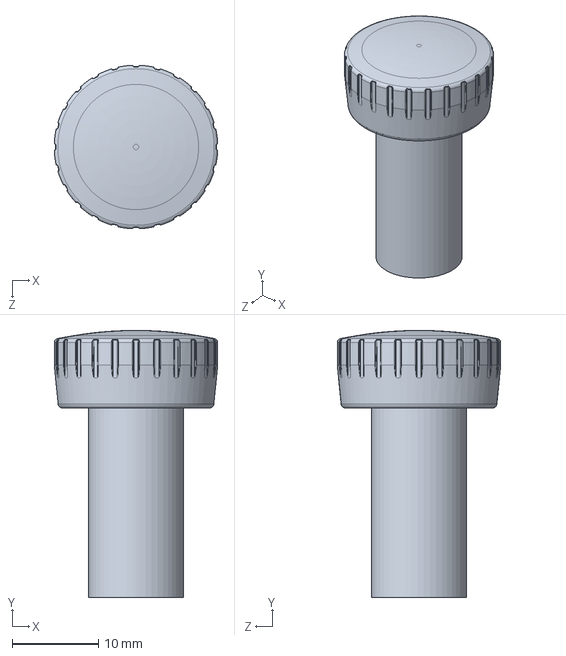
[picture p76: CAD file, 2022-10-12]
Model/Project/Кнопка.SLDPRT
19.0 x 31.0 x 19.0 mm
