ittuann/iGEM-2022-NEFU_China/Model/Project/金属舵盘.SLDPRT

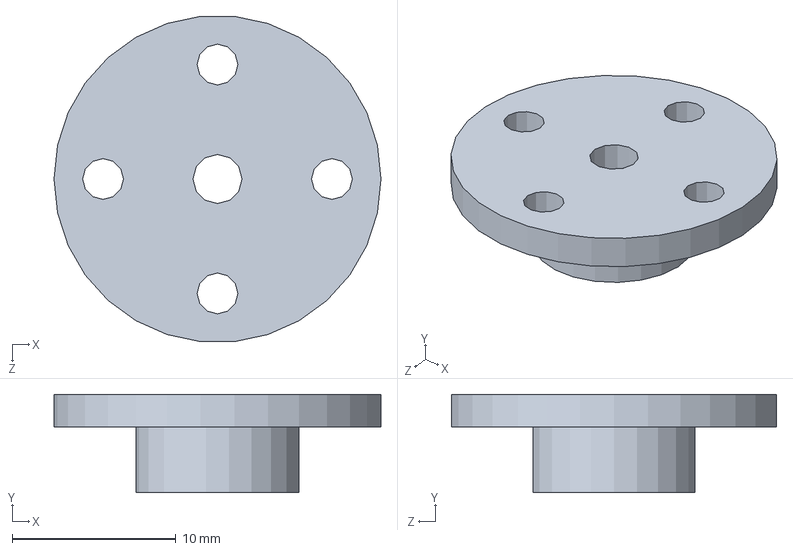
[picture p77: CAD file, 2022-10-12]
Model/Project/金属舵盘.SLDPRT
20.0 x 6.00 x 19.9 mm
