ittuann/iGEM-2022-NEFU_China/Model/Project/凸轮15x18.SLDPRT

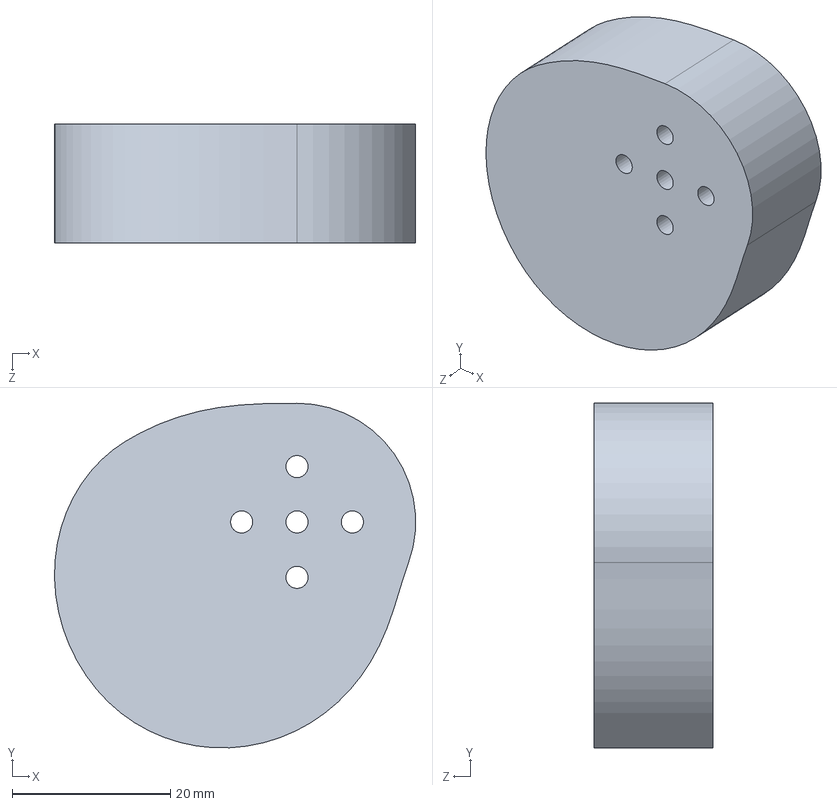
[picture p78: CAD file, 2022-10-12]
Model/Project/凸轮15x18.SLDPRT
45.6 x 43.5 x 15.0 mm
