ittuann/iGEM-2022-NEFU_China/Model/Project/舵盘.SLDPRT

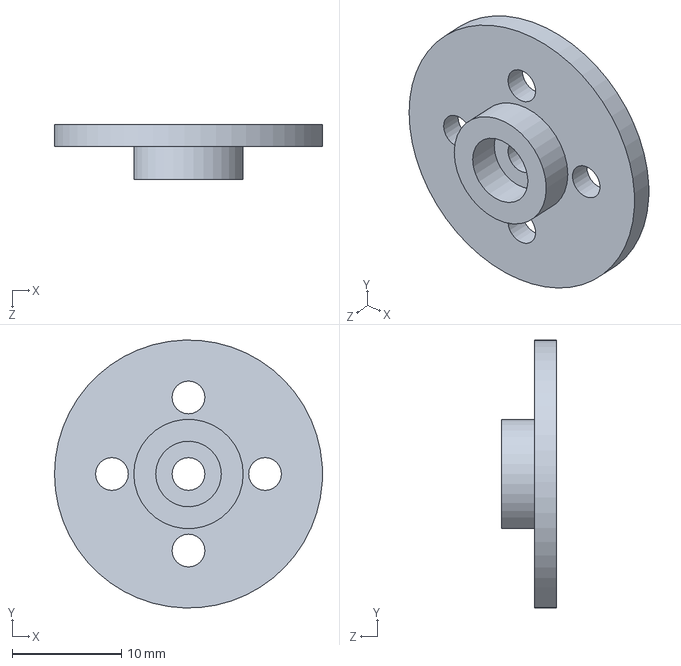
[picture p79: CAD file, 2022-10-12]
Model/Project/舵盘.SLDPRT
24.5 x 24.5 x 5.00 mm
