ittuann/iGEM-2022-NEFU_China/Model/Project/Экстрактор.SLDPRT

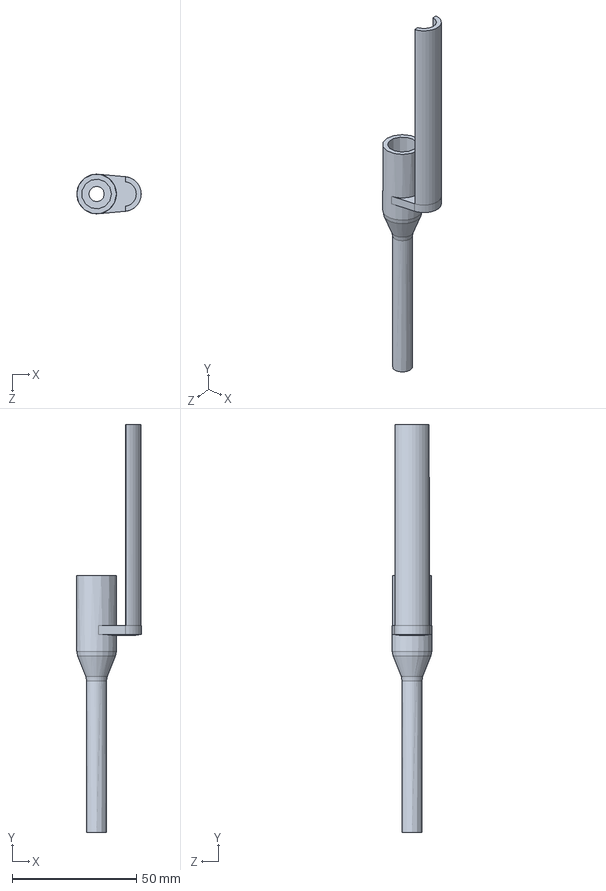
[picture p80: CAD file, 2022-10-12]
Model/Project/Экстрактор.SLDPRT
26.0 x 164.3 x 16.0 mm
