ittuann/iGEM-2022-NEFU_China/Model/Project/Дозатор пипеточный одноканальный.SLDASM

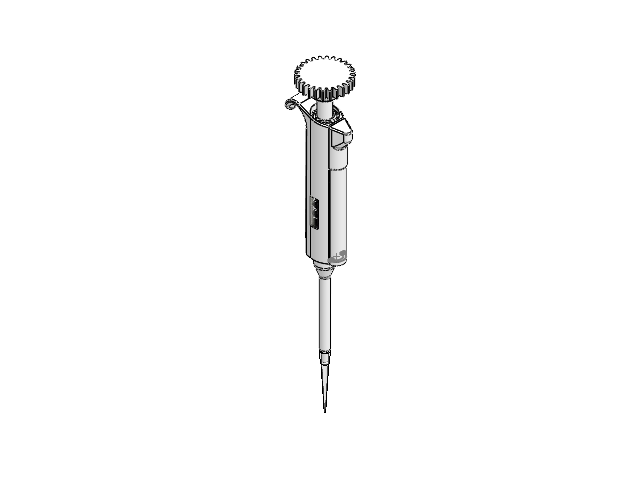
[picture p81: CAD file, 2022-10-12]
Model/Project/Дозатор пипеточный одноканальный.SLDASM
Корпус
Кнопка
Экстрактор
Игла
Кнопка экстрактора
Наконечник иглы
圆柱齿轮26×1.5
